levvayner/VGA_PLD/vga card/20250108_220106.jpg

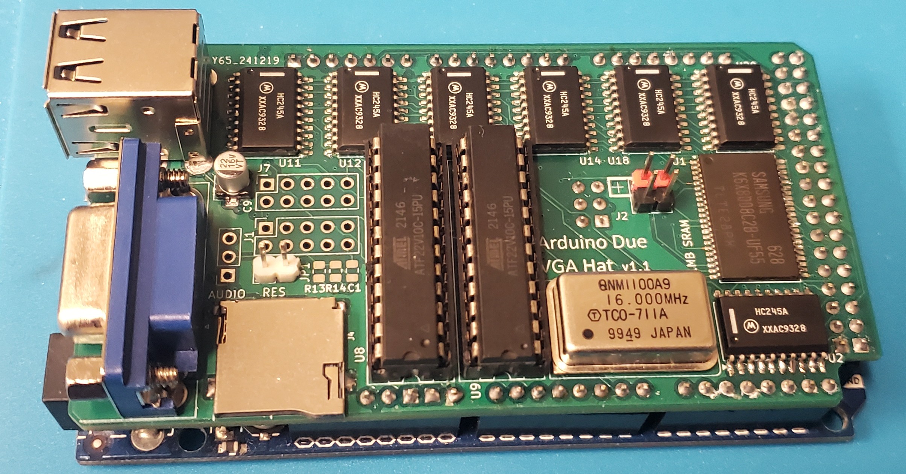
vga card/20250108_220106.jpg
