levvayner/VGA_PLD/vga card/20250108_220138.jpg

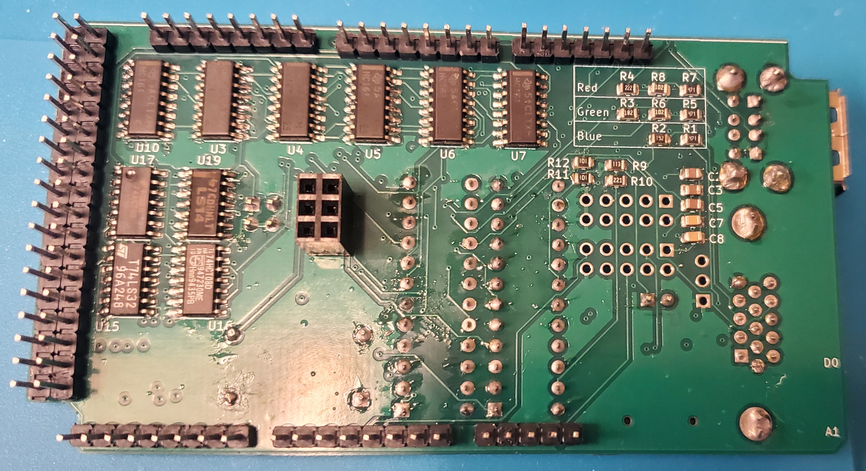
vga card/20250108_220138.jpg
